HasNate618/Object-Love-Interface/CAD/Export/Axle.STEP

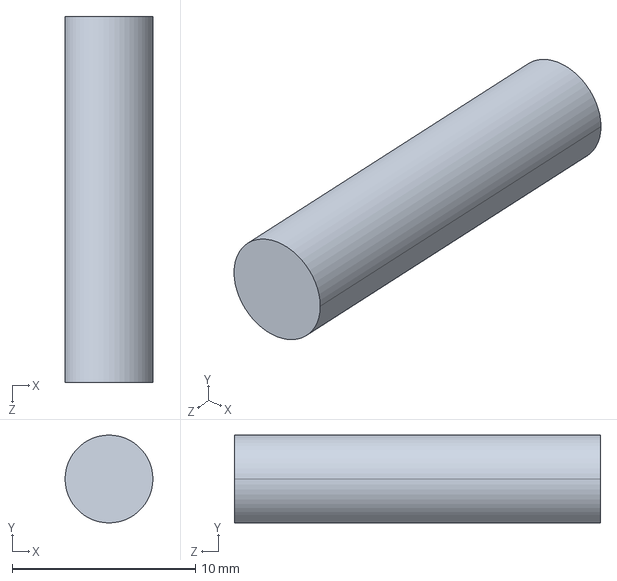
[picture p16: CAD file, 2026-02-15]
CAD/Export/Axle.STEP
4.80 x 4.80 x 20.0 mm
