HasNate618/Object-Love-Interface/CAD/Export/3D Print.3mf

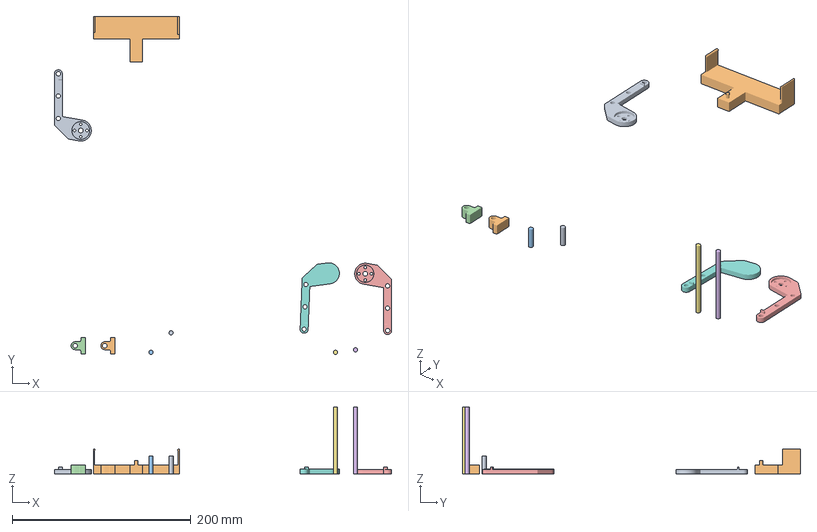
[picture p17: CAD file, 2026-02-15]
CAD/Export/3D Print.3mf
377.3 x 378.0 x 74.8 mm
Axle x 2
SnapClipAxleHolderSLDPRT x 2
Pivot Arm x 2
Arm Support Beam x 2
Pivot Arm(non powered)
SnapClip
