HasNate618/Object-Love-Interface/CAD/Main Assembly.SLDASM

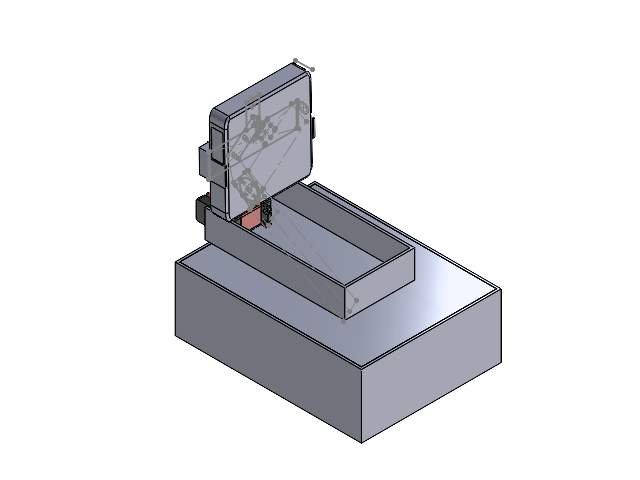
[picture p18: CAD file, 2026-02-15]
CAD/Main Assembly.SLDASM
Base
SenseCap Indicator D1
SnapClip
SnapClipAxleHolderSLDPRT x 2
TD-8135MG Servo
Pivot Arm
Base Cover
TableContainer
