HasNate618/Object-Love-Interface/Audio/m5core2_firmware/src/wifi_config.h

#pragma once

// WiFi credentials — edit these before flashing
#define WIFI_SSID     "espTest"
#define WIFI_PASSWORD "mkjy4040"

// HTTP control server port (M5Core2 listens on this)
#define HTTP_PORT     8082
